Xinyuan-LilyGO/T-TWR/examples/GPS_Full_Example/GPS_Full_Example.ino

/**
 * @file      GPS_Full_Example.ino
 * @author    Lewis He (lewishe@outlook.com)
 * @license   MIT
 * @copyright Copyright (c) 2024  Shenzhen Xin Yuan Electronic Technology Co., Ltd
 * @date      2024-01-05
 *
 */
#include <TinyGPS++.h>          //https://github.com/mikalhart/TinyGPSPlus
#include "LilyGo_TWR.h"


TinyGPSPlus gps;

void setup()
{
    Serial.begin(115200);

    // Initializing PMU is related to other peripherals
    twr.begin();

    if (twr.getVersion() == TWRClass::TWR_REV2V1) {
        Serial.println("Detection using TWR Rev2.1");
    } else {
        Serial.println("Detection using TWR Rev2.0");
    }

    Serial.println(F("FullExample.ino"));
    Serial.println(F("An extensive example of many interesting TinyGPS++ features"));
    Serial.print(F("Testing TinyGPS++ library v. ")); Serial.println(TinyGPSPlus::libraryVersion());
    Serial.println(F("by Mikal Hart"));
    Serial.println();
    Serial.println(F("Sats HDOP  Latitude   Longitude   Fix  Date       Time     Date Alt    Course Speed Card  Distance Course Card  Chars Sentences Checksum"));
    Serial.println(F("           (deg)      (deg)       Age                      Age  (m)    --- from GPS ----  ---- to London  ----  RX    RX        Fail"));
    Serial.println(F("----------------------------------------------------------------------------------------------------------------------------------------"));
}

void loop()
{
    static const double LONDON_LAT = 51.508131, LONDON_LON = -0.128002;

    printInt(gps.satellites.value(), gps.satellites.isValid(), 5);
    printFloat(gps.hdop.hdop(), gps.hdop.isValid(), 6, 1);
    printFloat(gps.location.lat(), gps.location.isValid(), 11, 6);
    printFloat(gps.location.lng(), gps.location.isValid(), 12, 6);
    printInt(gps.location.age(), gps.location.isValid(), 5);
    printDateTime(gps.date, gps.time);
    printFloat(gps.altitude.meters(), gps.altitude.isValid(), 7, 2);
    printFloat(gps.course.deg(), gps.course.isValid(), 7, 2);
    printFloat(gps.speed.kmph(), gps.speed.isValid(), 6, 2);
    printStr(gps.course.isValid() ? TinyGPSPlus::cardinal(gps.course.deg()) : "*** ", 6);

    unsigned long distanceKmToLondon =
        (unsigned long)TinyGPSPlus::distanceBetween(
            gps.location.lat(),
            gps.location.lng(),
            LONDON_LAT,
            LONDON_LON) / 1000;
    printInt(distanceKmToLondon, gps.location.isValid(), 9);

    double courseToLondon =
        TinyGPSPlus::courseTo(
            gps.location.lat(),
            gps.location.lng(),
            LONDON_LAT,
            LONDON_LON);

    printFloat(courseToLondon, gps.location.isValid(), 7, 2);

    const char *cardinalToLondon = TinyGPSPlus::cardinal(courseToLondon);

    printStr(gps.location.isValid() ? cardinalToLondon : "*** ", 6);

    printInt(gps.charsProcessed(), true, 6);
    printInt(gps.sentencesWithFix(), true, 10);
    printInt(gps.failedChecksum(), true, 9);
    Serial.println();

    smartDelay(1000);

    if (millis() > 5000 && gps.charsProcessed() < 10)
        Serial.println(F("No GPS data received: check wiring"));
}

// This custom version of delay() ensures that the gps object
// is being "fed".
static void smartDelay(unsigned long ms)
{
    unsigned long start = millis();
    do {
        while (GPSSerial.available()) {
            gps.encode(GPSSerial.read());
        }
    } while (millis() - start < ms);
}

static void printFloat(float val, bool valid, int len, int prec)
{
    if (!valid) {
        while (len-- > 1)
            Serial.print('*');
        Serial.print(' ');
    } else {
        Serial.print(val, prec);
        int vi = abs((int)val);
        int flen = prec + (val < 0.0 ? 2 : 1); // . and -
        flen += vi >= 1000 ? 4 : vi >= 100 ? 3 : vi >= 10 ? 2 : 1;
        for (int i = flen; i < len; ++i)
            Serial.print(' ');
    }
    smartDelay(0);
}

static void printInt(unsigned long val, bool valid, int len)
{
    char sz[32] = "*****************";
    if (valid)
        sprintf(sz, "%ld", val);
    sz[len] = 0;
    for (int i = strlen(sz); i < len; ++i)
        sz[i] = ' ';
    if (len > 0)
        sz[len - 1] = ' ';
    Serial.print(sz);
    smartDelay(0);
}

static void printDateTime(TinyGPSDate &d, TinyGPSTime &t)
{
    if (!d.isValid()) {
        Serial.print(F("********** "));
    } else {
        char sz[32];
        sprintf(sz, "%02d/%02d/%02d ", d.month(), d.day(), d.year());
        Serial.print(sz);
    }

    if (!t.isValid()) {
        Serial.print(F("******** "));
    } else {
        char sz[32];
        sprintf(sz, "%02d:%02d:%02d ", t.hour(), t.minute(), t.second());
        Serial.print(sz);
    }

    printInt(d.age(), d.isValid(), 5);
    smartDelay(0);
}

static void printStr(const char *str, int len)
{
    int slen = strlen(str);
    for (int i = 0; i < len; ++i)
        Serial.print(i < slen ? str[i] : ' ');
    smartDelay(0);
}
