Xinyuan-LilyGO/T-TWR/examples/GPS_Basic_Example/GPS_Basic_Example.ino

/**
 * @file      GPS_Basic_Example.ino
 * @author    Lewis He (lewishe@outlook.com)
 * @license   MIT
 * @copyright Copyright (c) 2024  Shenzhen Xin Yuan Electronic Technology Co., Ltd
 * @date      2024-01-05
 *
 */
#include <TinyGPS++.h>          //https://github.com/mikalhart/TinyGPSPlus
#include "LilyGo_TWR.h"

TinyGPSPlus gps;

void setup()
{
    Serial.begin(115200);

    // Initializing PMU is related to other peripherals
    twr.begin();

    if (twr.getVersion() == TWRClass::TWR_REV2V1) {
        Serial.println("Detection using TWR Rev2.1");
    } else {
        Serial.println("Detection using TWR Rev2.0");
    }

    Serial.println(F("BasicExample.ino"));
    Serial.println(F("Basic demonstration of TinyGPS++ (no device needed)"));
    Serial.print(F("Testing TinyGPS++ library v. ")); Serial.println(TinyGPSPlus::libraryVersion());
    Serial.println(F("by Mikal Hart"));
    Serial.println();
}

void loop()
{
    while (GPSSerial.available()) {
        if (gps.encode(GPSSerial.read())) {
            displayInfo();
        }
    }
    delay(2);
}

void displayInfo()
{
    Serial.print(F("Location: "));
    if (gps.location.isValid()) {
        Serial.print(gps.location.lat(), 6);
        Serial.print(F(","));
        Serial.print(gps.location.lng(), 6);
    } else {
        Serial.print(F("INVALID"));
    }

    Serial.print(F("  Date/Time: "));
    if (gps.date.isValid()) {
        Serial.print(gps.date.month());
        Serial.print(F("/"));
        Serial.print(gps.date.day());
        Serial.print(F("/"));
        Serial.print(gps.date.year());
    } else {
        Serial.print(F("INVALID"));
    }

    Serial.print(F(" "));
    if (gps.time.isValid()) {
        if (gps.time.hour() < 10) Serial.print(F("0"));
        Serial.print(gps.time.hour());
        Serial.print(F(":"));
        if (gps.time.minute() < 10) Serial.print(F("0"));
        Serial.print(gps.time.minute());
        Serial.print(F(":"));
        if (gps.time.second() < 10) Serial.print(F("0"));
        Serial.print(gps.time.second());
        Serial.print(F("."));
        if (gps.time.centisecond() < 10) Serial.print(F("0"));
        Serial.print(gps.time.centisecond());
    } else {
        Serial.print(F("INVALID"));
    }

    Serial.println();
}
