Xinyuan-LilyGO/T-TWR/examples/Factory/Constants.h

#pragma once

#include <pgmspace.h>
#include <stdint.h>

#define COUNT(x)                    sizeof(x)/sizeof(*x)

const unsigned char  xbmLOGO[] PROGMEM = {
    0x00, 0x00, 0x00, 0x00, 0x00, 0x00, 0x00, 0x00, 0x00, 0x00, 0x00, 0x00, 0x00, 0x00, 0x00,
    0x00, 0x00, 0x00, 0x60, 0x00, 0x00, 0x00, 0x00, 0x06, 0xe0, 0x03, 0x00, 0x00, 0xc0, 0x07,
    0xf0, 0x0f, 0x00, 0x00, 0xf8, 0x07, 0xf0, 0x3f, 0x00, 0x00, 0xfc, 0x0f, 0xf0, 0x7f, 0x00,
    0x00, 0xff, 0x0f, 0xf0, 0xff, 0xf9, 0x9f, 0xff, 0x0f, 0xf8, 0xff, 0xff, 0xff, 0xff, 0x0f,
    0xf8, 0xff, 0xff, 0xff, 0xff, 0x0f, 0xf8, 0xff, 0xff, 0xff, 0xff, 0x1f, 0xf8, 0xff, 0xff,
    0xff, 0xff, 0x1f, 0xf8, 0xff, 0xff, 0xff, 0xff, 0x1f, 0xf8, 0xff, 0xff, 0xff, 0xff, 0x1f,
    0xf8, 0xff, 0xff, 0xff, 0xff, 0x1f, 0xfc, 0xff, 0xff, 0xff, 0xff, 0x3f, 0xfe, 0xff, 0xff,
    0xff, 0xff, 0x3f, 0xfe, 0xff, 0xff, 0xff, 0xff, 0x7f, 0xfe, 0xff, 0xff, 0xff, 0xff, 0x7f,
    0xff, 0xff, 0xff, 0xff, 0xff, 0xff, 0xff, 0xff, 0xff, 0xff, 0xff, 0xff, 0xff, 0xff, 0xff,
    0xff, 0xff, 0xff, 0xff, 0xff, 0xff, 0xff, 0xff, 0xff, 0xff, 0x07, 0x00, 0x00, 0xe0, 0xff,
    0xff, 0x01, 0x00, 0x00, 0x80, 0xff, 0xff, 0x01, 0x00, 0x00, 0x00, 0xff, 0xff, 0xc0, 0x01,
    0xc0, 0x03, 0xff, 0x7f, 0xe0, 0x03, 0xe0, 0x07, 0xfe, 0x7f, 0xf0, 0x07, 0xe0, 0x0f, 0xfe,
    0x7f, 0xf0, 0x0f, 0xf0, 0x0f, 0xfe, 0x7f, 0xf0, 0x0f, 0xf0, 0x0f, 0xfe, 0x7f, 0xf0, 0x0f,
    0xf0, 0x0f, 0xfe, 0x7e, 0xf0, 0x0f, 0xf0, 0x0f, 0xfe, 0x7e, 0xf0, 0x07, 0xe0, 0x0f, 0x7e,
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
const unsigned char xMenuRight[]  PROGMEM = { /*10x10px*/ 0x1c, 0x00, 0x38, 0x00, 0x70, 0x00, 0xe0, 0x00, 0xc0, 0x01, 0xc0, 0x01, 0xe0, 0x00, 0x70, 0x00, 0x38, 0x00, 0x1c, 0x00 };
